adamgreig/walkclock-public/artwork/shikoku/crops/0.jpg

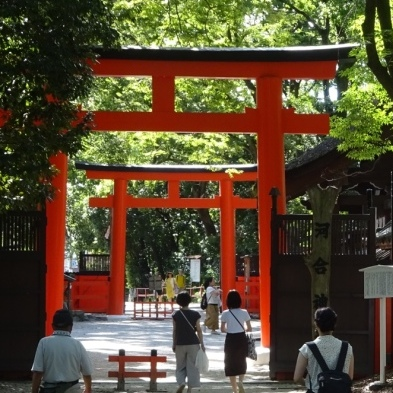
artwork/shikoku/crops/0.jpg
