adamgreig/walkclock-public/artwork/shikoku/crops/1.jpg

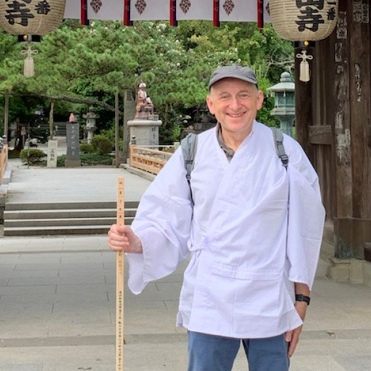
artwork/shikoku/crops/1.jpg
