adamgreig/walkclock-public/artwork/shikoku/crops/2.jpg

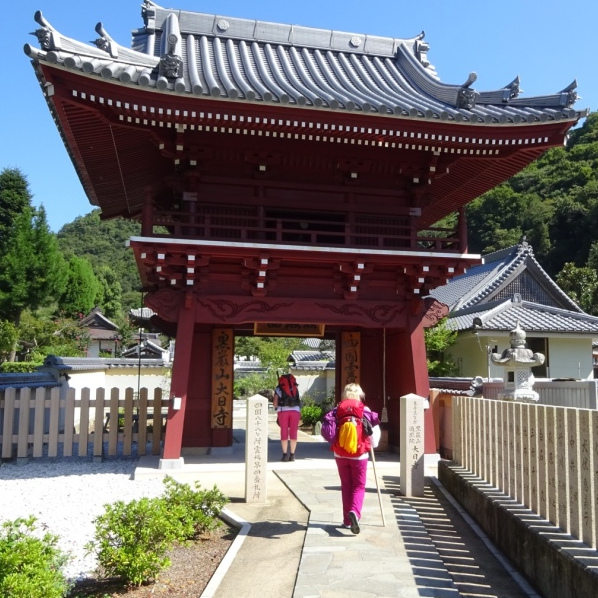
artwork/shikoku/crops/2.jpg
