adamgreig/walkclock-public/artwork/shikoku/crops/3.jpg

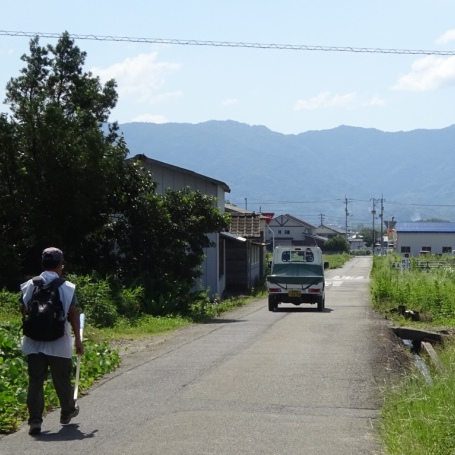
artwork/shikoku/crops/3.jpg
