adamgreig/walkclock-public/artwork/shikoku/crops/4.jpg

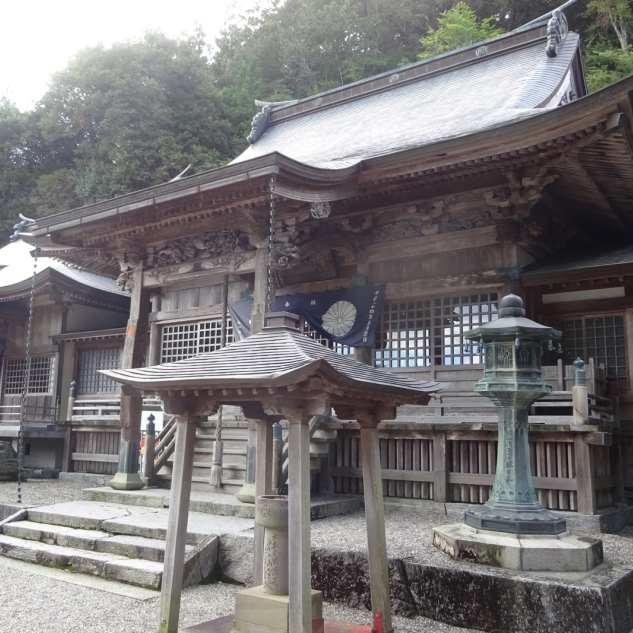
artwork/shikoku/crops/4.jpg
