adamgreig/walkclock-public/artwork/shikoku/crops/5.jpg

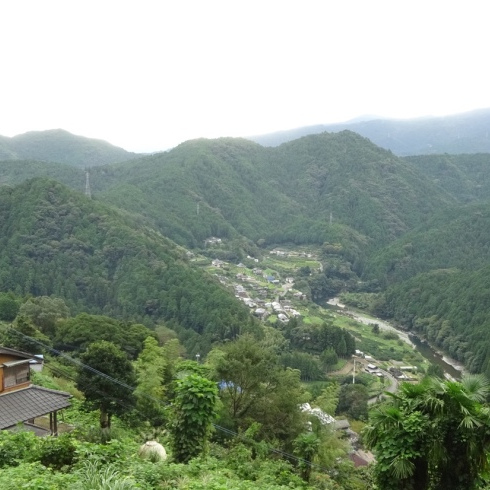
artwork/shikoku/crops/5.jpg
