adamgreig/walkclock-public/artwork/shikoku/crops/6.jpg

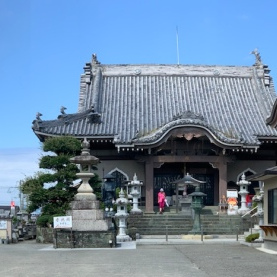
artwork/shikoku/crops/6.jpg
