adamgreig/walkclock-public/artwork/shikoku/crops/7.jpg

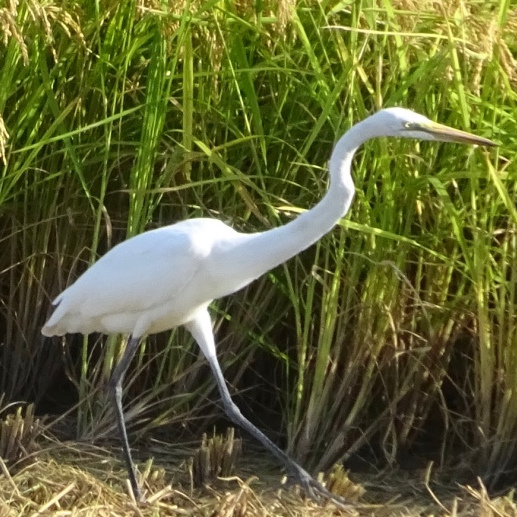
artwork/shikoku/crops/7.jpg
