adamgreig/walkclock-public/artwork/shikoku/crops/8.jpg

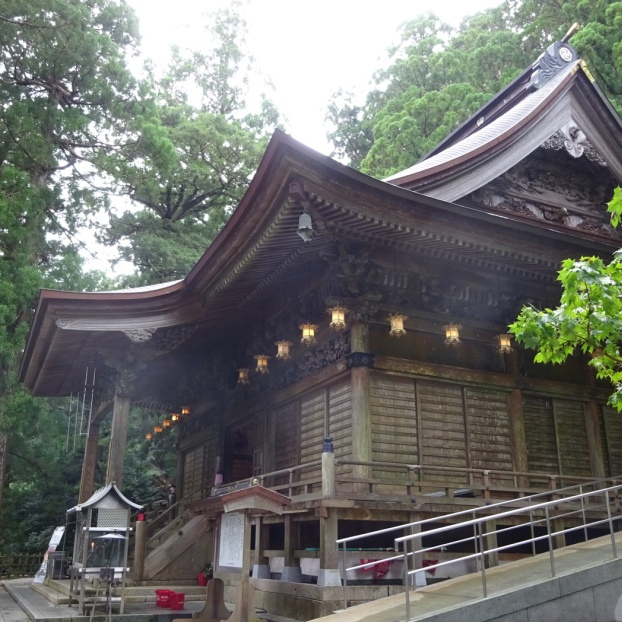
artwork/shikoku/crops/8.jpg
