adamgreig/walkclock-public/artwork/shikoku/crops/9.jpg

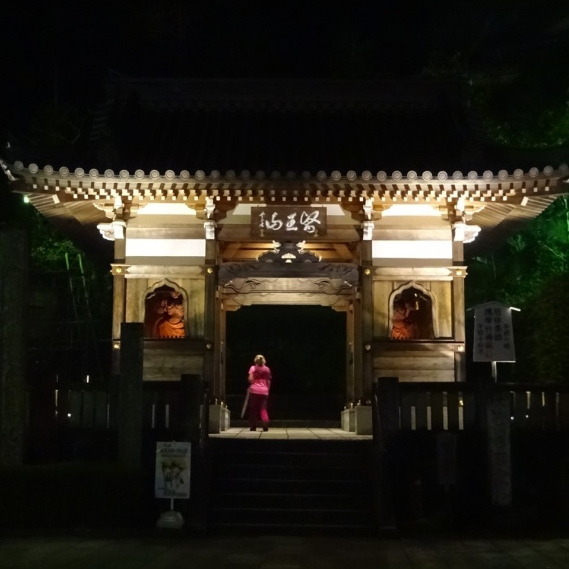
artwork/shikoku/crops/9.jpg
