adamgreig/walkclock-public/artwork/shikoku/crops/10.jpg

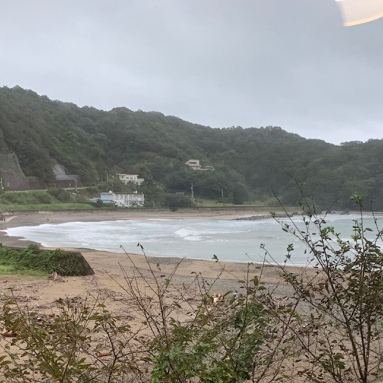
artwork/shikoku/crops/10.jpg
