adamgreig/walkclock-public/artwork/shikoku/crops/11.jpg

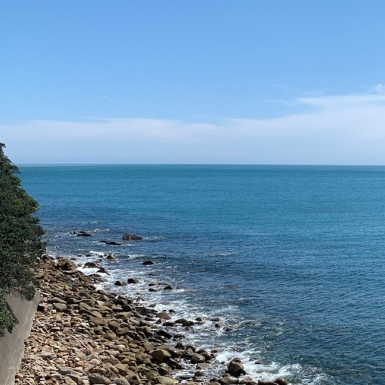
artwork/shikoku/crops/11.jpg
