adamgreig/walkclock-public/artwork/shikoku/crops/12.jpg

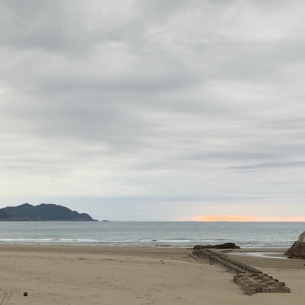
artwork/shikoku/crops/12.jpg
