adamgreig/walkclock-public/artwork/shikoku/crops/13.jpg

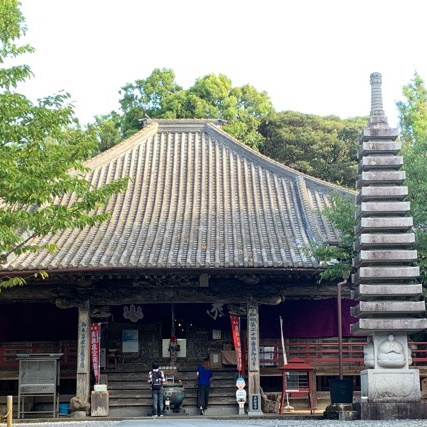
artwork/shikoku/crops/13.jpg
