adamgreig/walkclock-public/artwork/shikoku/crops/14.jpg

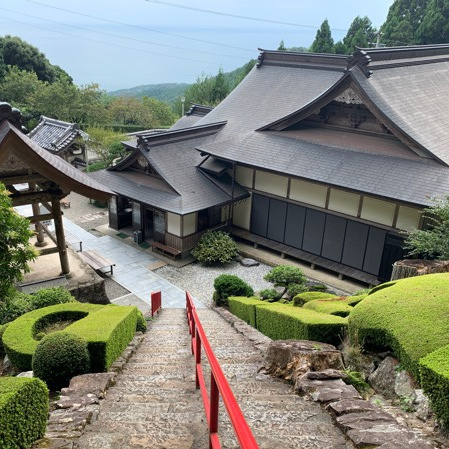
artwork/shikoku/crops/14.jpg
