adamgreig/walkclock-public/artwork/shikoku/crops/15.jpg

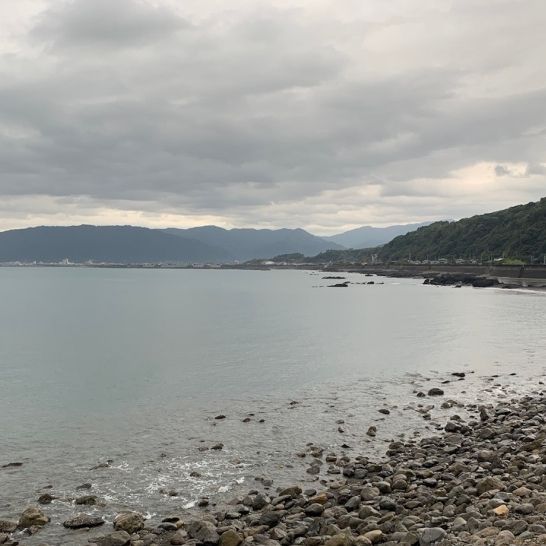
artwork/shikoku/crops/15.jpg
