adamgreig/walkclock-public/artwork/shikoku/crops/16.jpg

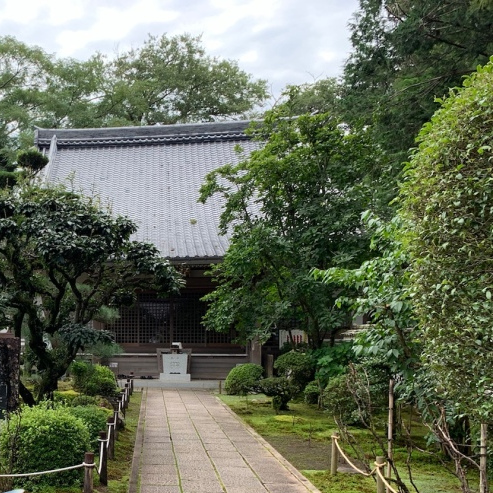
artwork/shikoku/crops/16.jpg
