adamgreig/walkclock-public/artwork/shikoku/crops/17.jpg

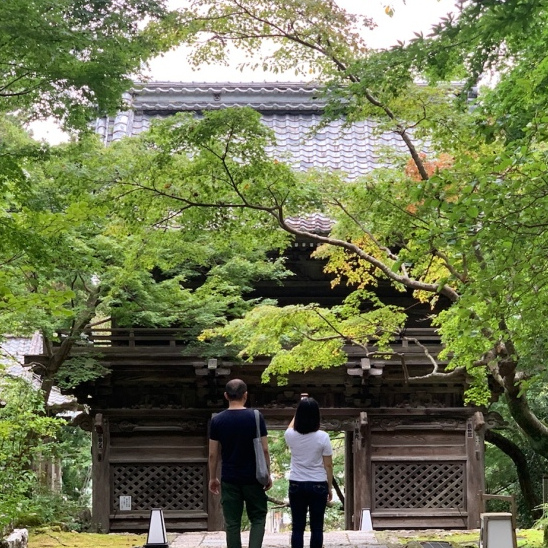
artwork/shikoku/crops/17.jpg
