adamgreig/walkclock-public/artwork/shikoku/crops/18.jpg

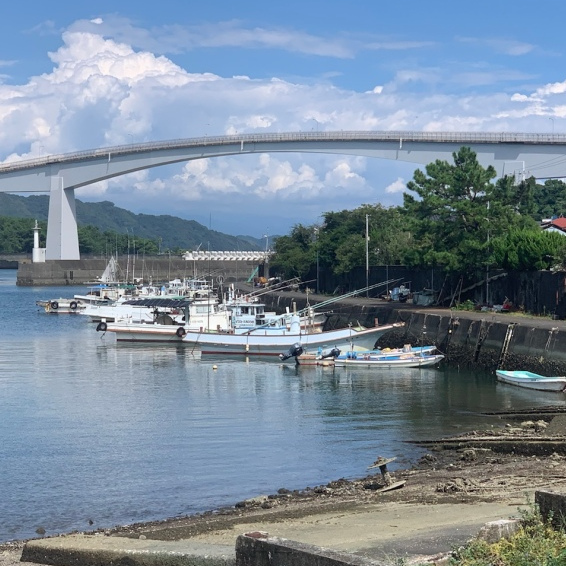
artwork/shikoku/crops/18.jpg
