adamgreig/walkclock-public/artwork/shikoku/crops/19.jpg

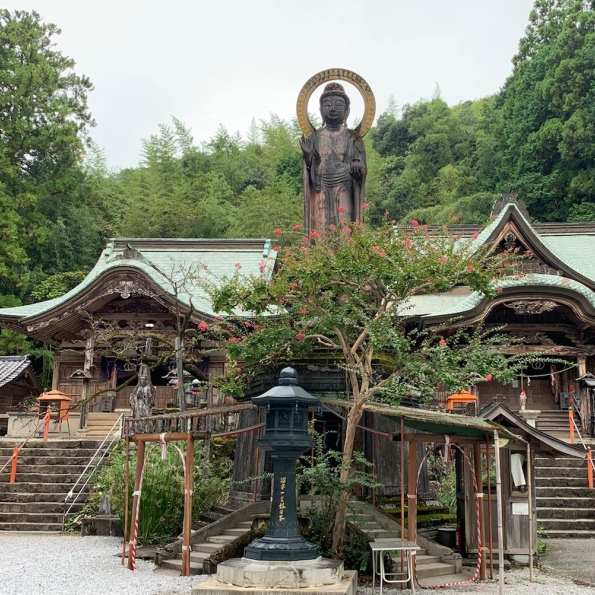
artwork/shikoku/crops/19.jpg
