adamgreig/walkclock-public/artwork/shikoku/crops/20.jpg

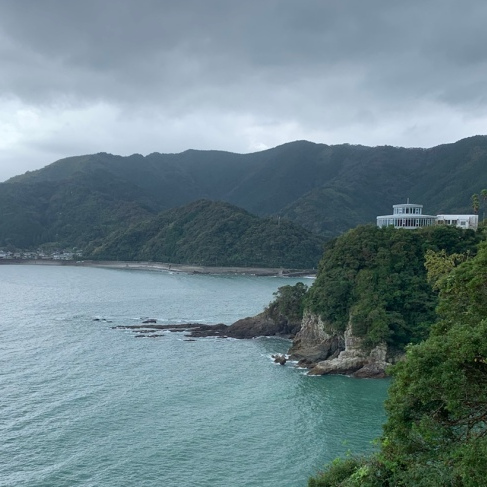
artwork/shikoku/crops/20.jpg
