adamgreig/walkclock-public/artwork/shikoku/crops/21.jpg

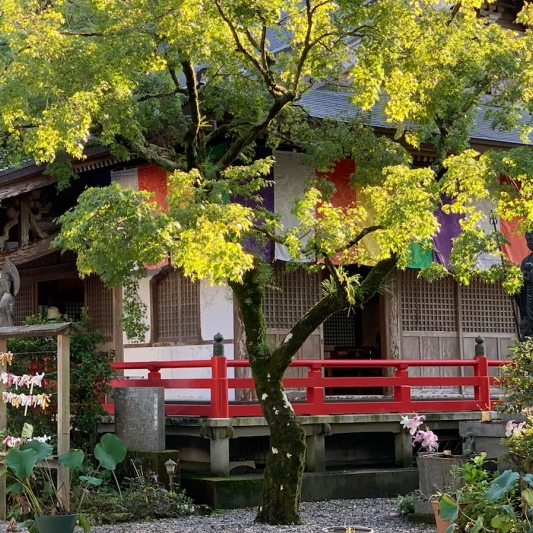
artwork/shikoku/crops/21.jpg
