adamgreig/walkclock-public/artwork/shikoku/crops/22.jpg

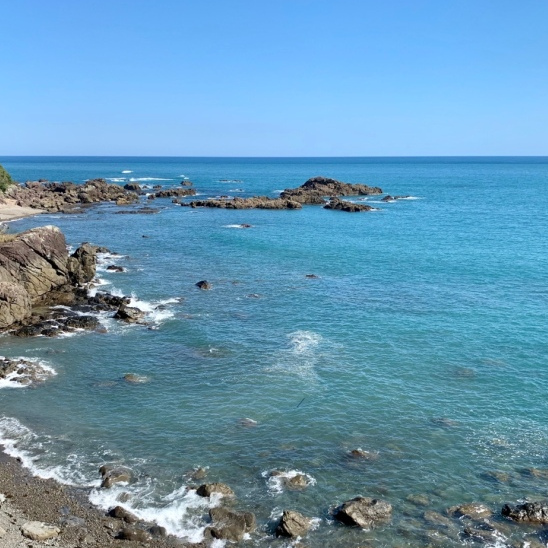
artwork/shikoku/crops/22.jpg
