adamgreig/walkclock-public/artwork/shikoku/crops/23.jpg

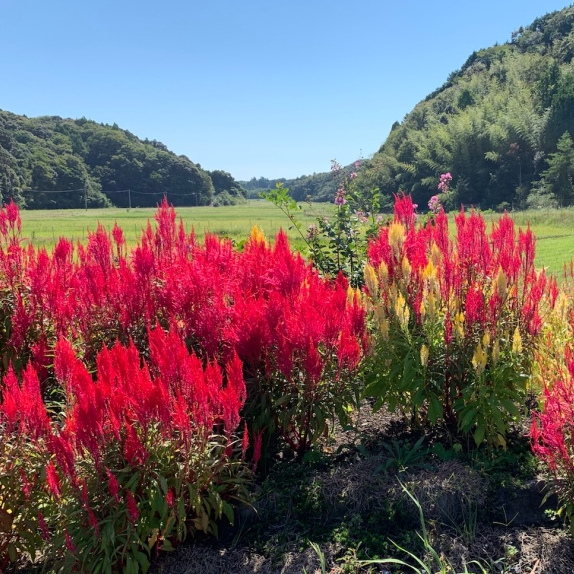
artwork/shikoku/crops/23.jpg
