adamgreig/walkclock-public/artwork/shikoku/crops/24.jpg

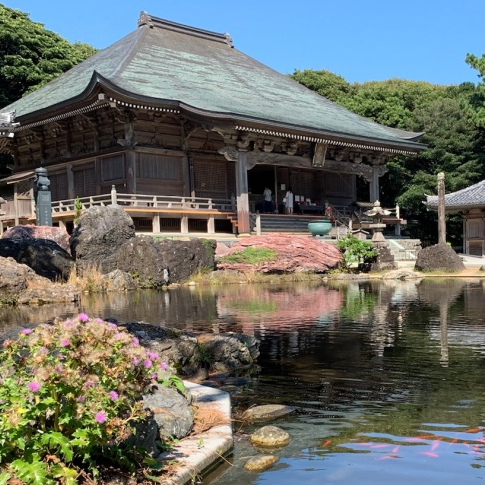
artwork/shikoku/crops/24.jpg
