adamgreig/walkclock-public/artwork/shikoku/crops/25.jpg

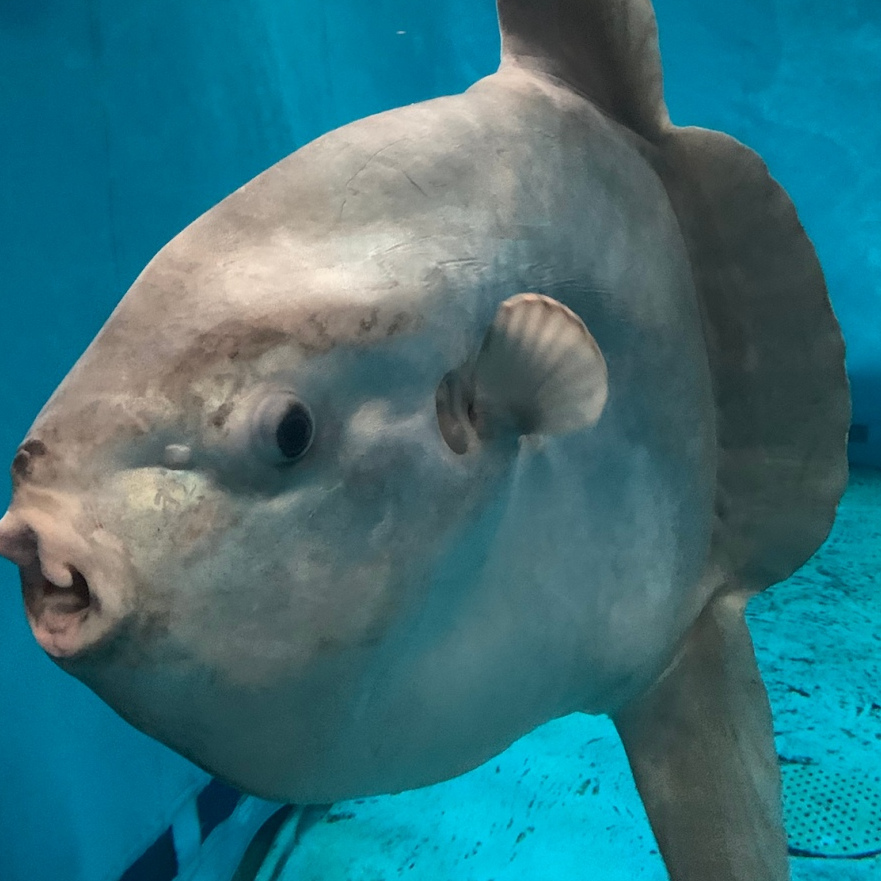
artwork/shikoku/crops/25.jpg
