adamgreig/walkclock-public/artwork/shikoku/crops/26.jpg

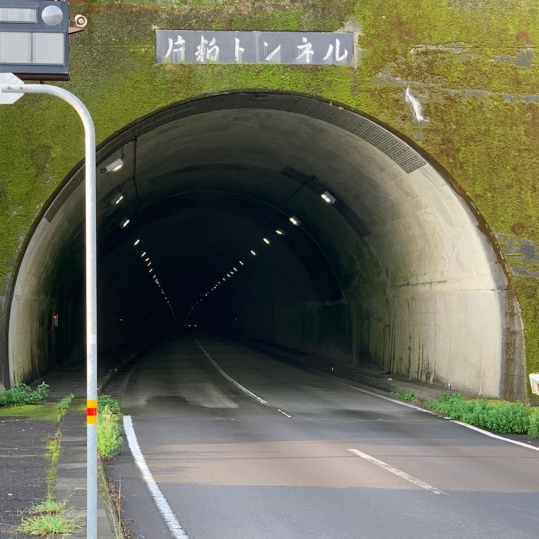
artwork/shikoku/crops/26.jpg
