adamgreig/walkclock-public/artwork/shikoku/crops/27.jpg

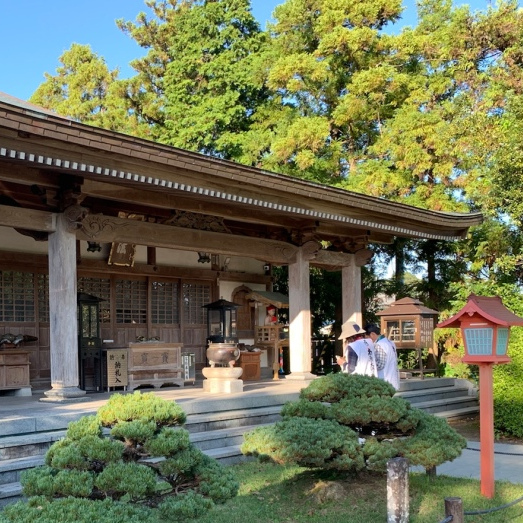
artwork/shikoku/crops/27.jpg
