adamgreig/walkclock-public/artwork/shikoku/crops/28.jpg

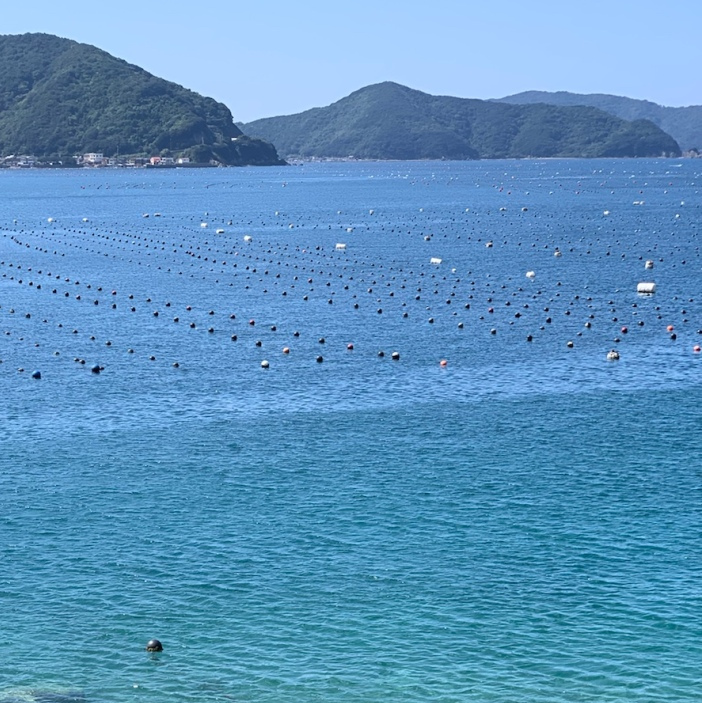
artwork/shikoku/crops/28.jpg
