adamgreig/walkclock-public/artwork/shikoku/crops/29.jpg

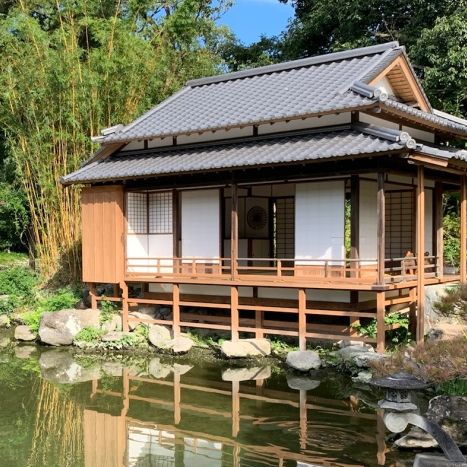
artwork/shikoku/crops/29.jpg
