adamgreig/walkclock-public/artwork/shikoku/crops/30.jpg

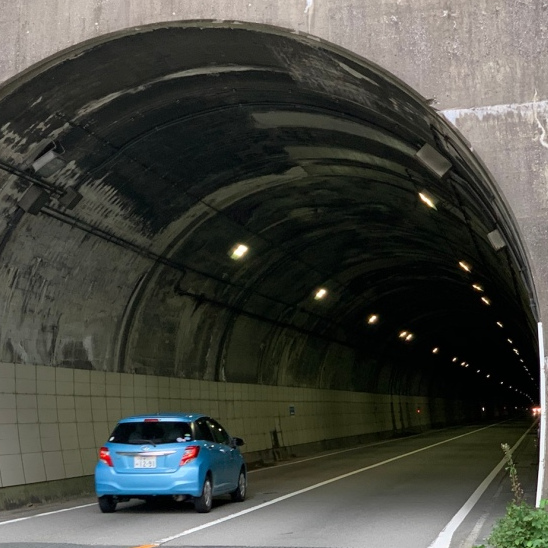
artwork/shikoku/crops/30.jpg
