adamgreig/walkclock-public/artwork/shikoku/crops/31.jpg

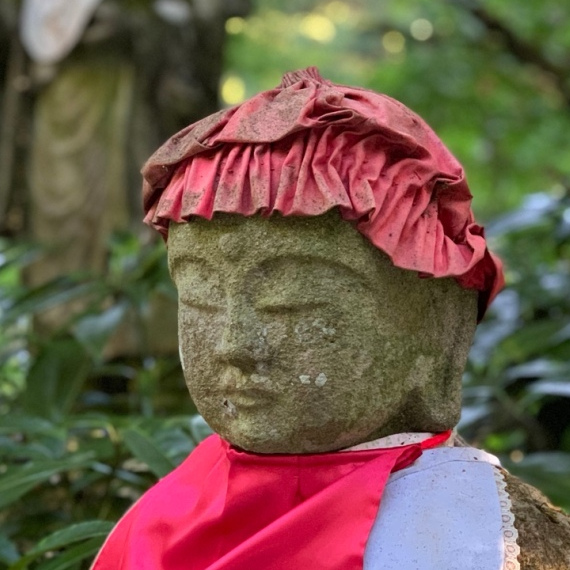
artwork/shikoku/crops/31.jpg
