adamgreig/walkclock-public/artwork/shikoku/crops/32.jpg

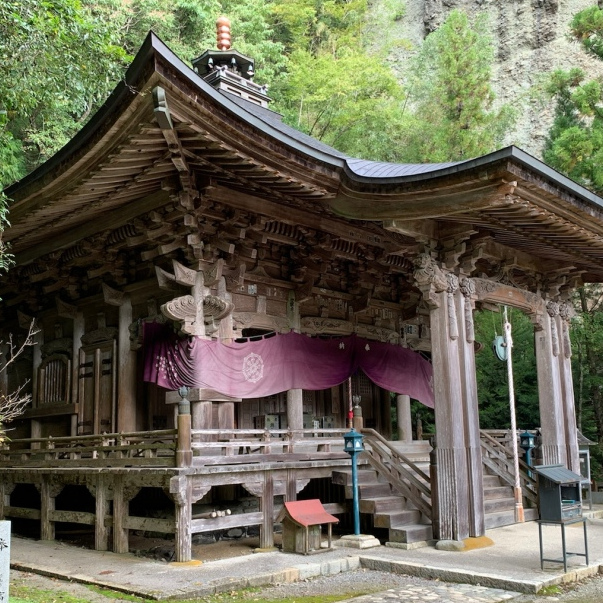
artwork/shikoku/crops/32.jpg
