adamgreig/walkclock-public/artwork/shikoku/crops/33.jpg

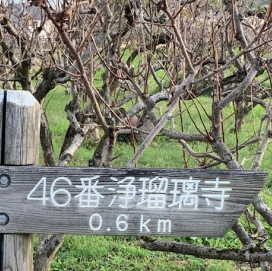
artwork/shikoku/crops/33.jpg
