adamgreig/walkclock-public/artwork/shikoku/crops/34.jpg

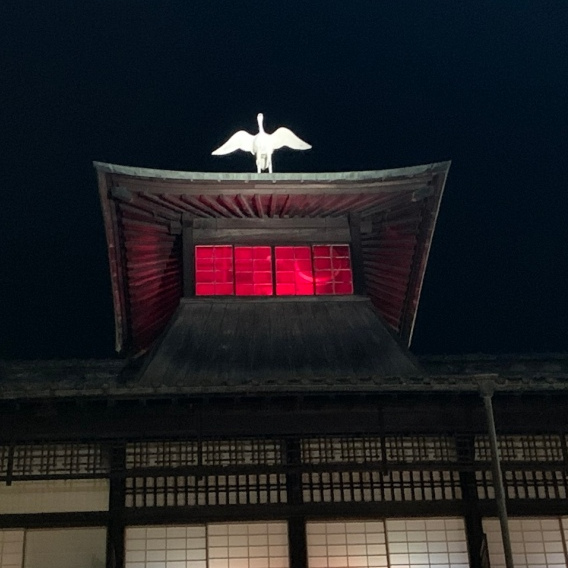
artwork/shikoku/crops/34.jpg
