adamgreig/walkclock-public/artwork/shikoku/crops/35.jpg

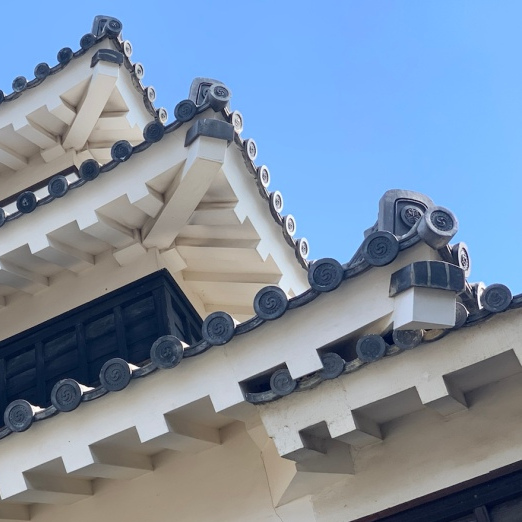
artwork/shikoku/crops/35.jpg
