adamgreig/walkclock-public/artwork/shikoku/crops/36.jpg

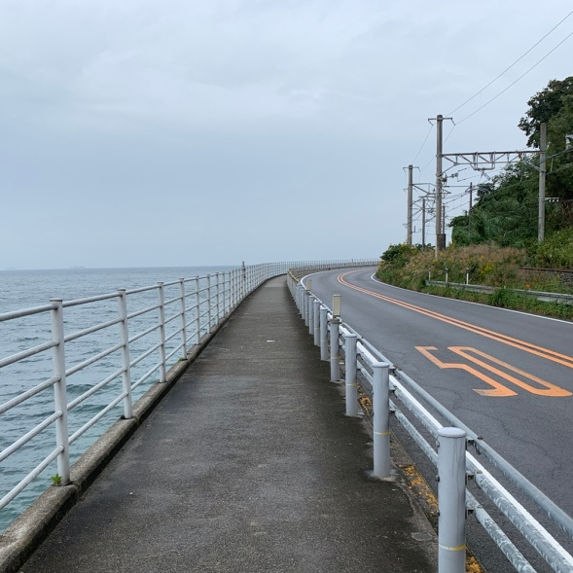
artwork/shikoku/crops/36.jpg
