adamgreig/walkclock-public/artwork/shikoku/crops/37.jpg

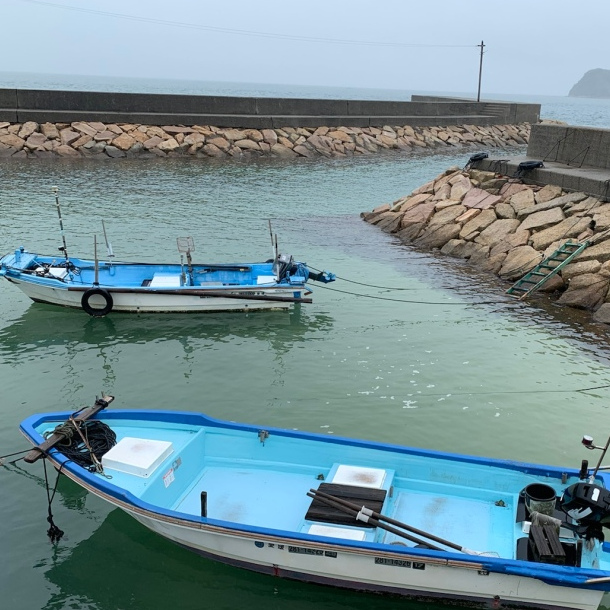
artwork/shikoku/crops/37.jpg
