adamgreig/walkclock-public/artwork/shikoku/crops/38.jpg

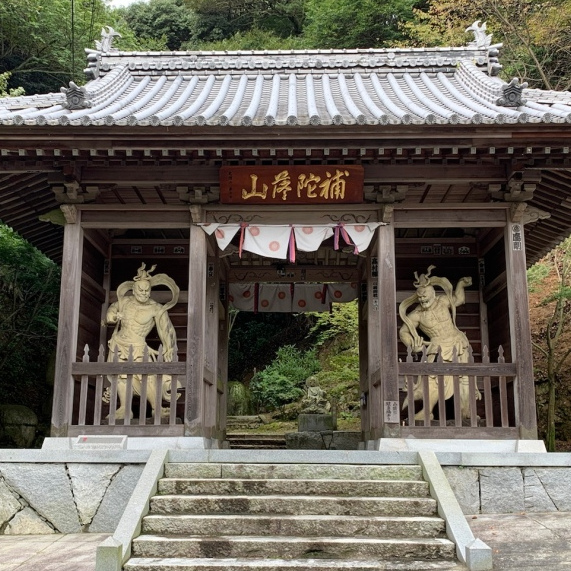
artwork/shikoku/crops/38.jpg
