adamgreig/walkclock-public/artwork/shikoku/crops/39.jpg

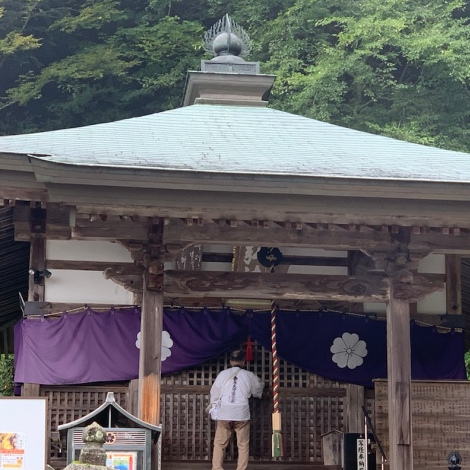
artwork/shikoku/crops/39.jpg
