adamgreig/walkclock-public/artwork/shikoku/crops/40.jpg

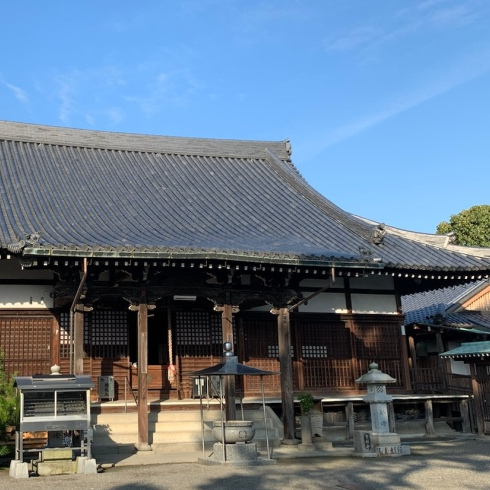
artwork/shikoku/crops/40.jpg
