adamgreig/walkclock-public/artwork/shikoku/crops/41.jpg

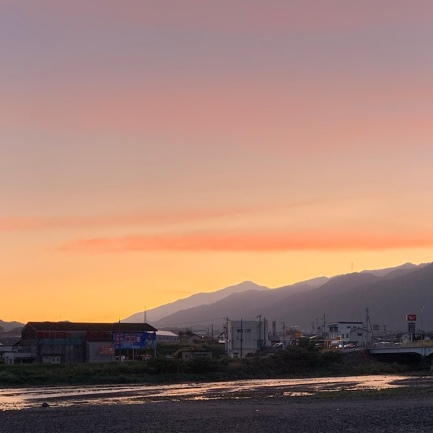
artwork/shikoku/crops/41.jpg
