adamgreig/walkclock-public/artwork/shikoku/crops/42.jpg

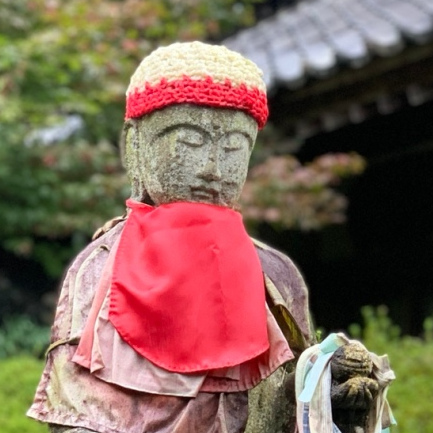
artwork/shikoku/crops/42.jpg
