adamgreig/walkclock-public/artwork/shikoku/crops/43.jpg

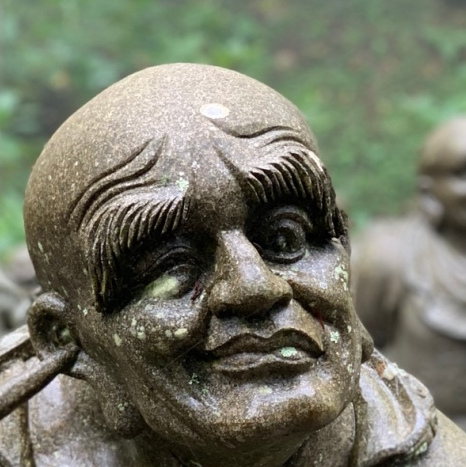
artwork/shikoku/crops/43.jpg
