adamgreig/walkclock-public/artwork/shikoku/crops/44.jpg

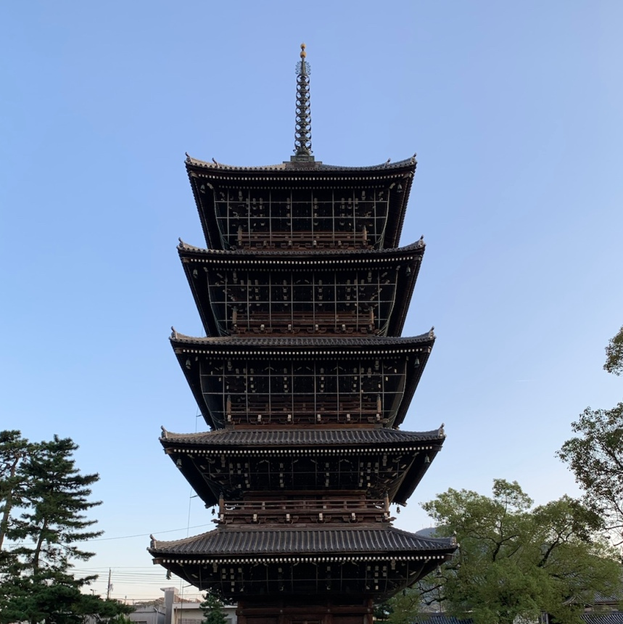
artwork/shikoku/crops/44.jpg
