adamgreig/walkclock-public/artwork/shikoku/crops/45.jpg

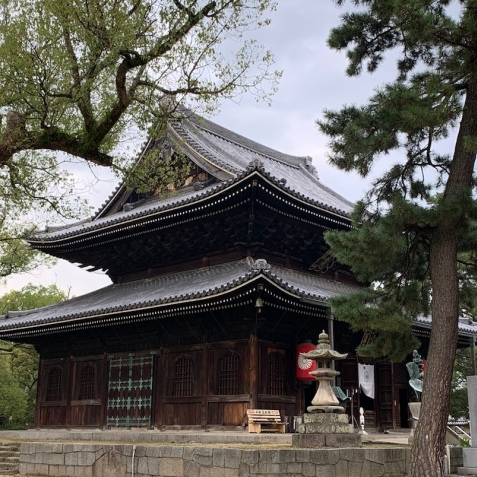
artwork/shikoku/crops/45.jpg
