adamgreig/walkclock-public/artwork/shikoku/crops/46.jpg

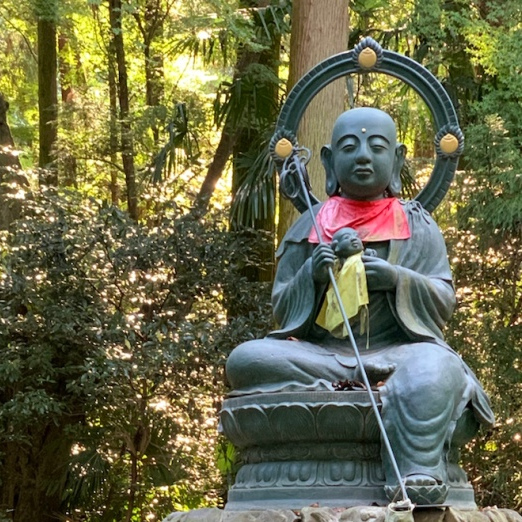
artwork/shikoku/crops/46.jpg
