adamgreig/walkclock-public/artwork/shikoku/crops/47.jpg

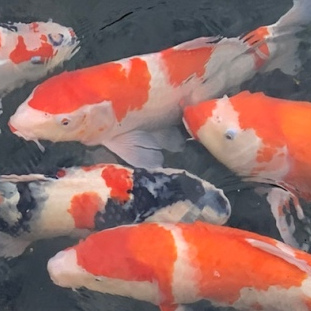
artwork/shikoku/crops/47.jpg
