adamgreig/walkclock-public/artwork/shikoku/crops/48.jpg

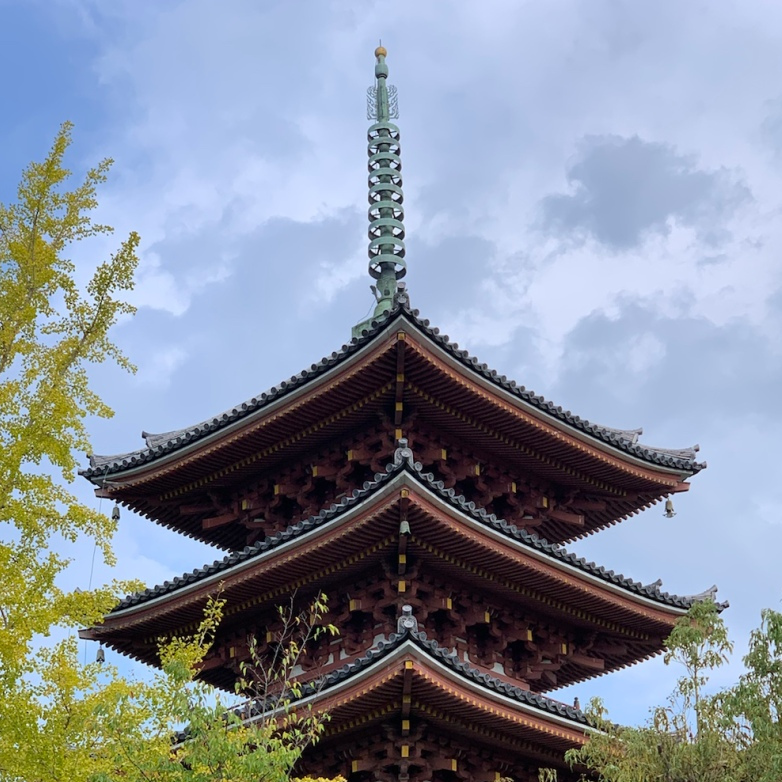
artwork/shikoku/crops/48.jpg
