adamgreig/walkclock-public/artwork/shikoku/crops/49.jpg

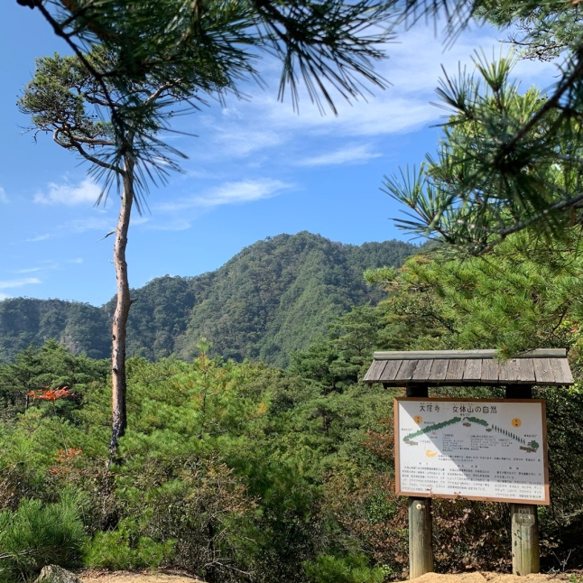
artwork/shikoku/crops/49.jpg
