adamgreig/walkclock-public/artwork/shikoku/crops/50.jpg

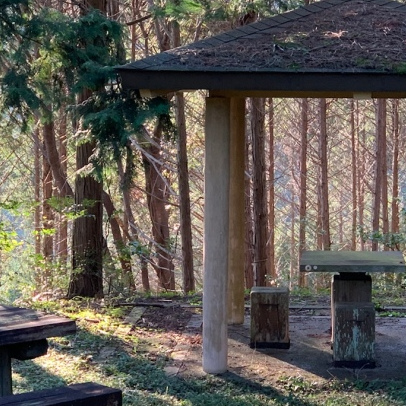
artwork/shikoku/crops/50.jpg
