adamgreig/walkclock-public/artwork/shikoku/crops/51.jpg

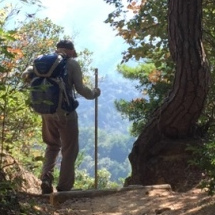
artwork/shikoku/crops/51.jpg
